AndyD87/LED-Cube-8x8x8-RGB/Software/PIC18F4520/config.h

/**
 * @file    config.h
 * @author  Andreas Dirmeier
 * @version 0.01
 *  
 * @brief   Configuration Bits and Functions for uController
 */
#ifndef CONFIG_H
#define	CONFIG_H

#include <xc.h>

// #pragma config statements should precede project file includes.
// Use project enums instead of #define for ON and OFF.

// CONFIG1H
#pragma config OSC = HS         /**< Oscillator Selection bits (HS oscillator)*/
#pragma config FCMEN = OFF      // Fail-Safe Clock Monitor Enable bit (Fail-Safe Clock Monitor disabled)*/
#pragma config IESO = OFF       /**< Internal/External Oscillator Switchover bit (Oscillator Switchover mode disabled)*/

// CONFIG2L
#pragma config PWRT = OFF       /**< Power-up Timer Enable bit (PWRT disabled)*/
#pragma config BOREN = OFF      /**< Brown-out Reset Enable bits (Brown-out Reset disabled in hardware and software)*/
#pragma config BORV = 0         /**< Brown Out Reset Voltage bits (Maximum setting)*/

// CONFIG2H
#pragma config WDT = OFF        /**< Watchdog Timer Enable bit (WDT disabled (control is placed on the SWDTEN bit))*/
#pragma config WDTPS = 32768    /**< Watchdog Timer Postscale Select bits (1:32768)*/

// CONFIG3H
#pragma config CCP2MX = PORTC   /**< CCP2 MUX bit (CCP2 input/output is multiplexed with RC1)*/
#pragma config PBADEN = OFF     /**< PORTB A/D Enable bit (PORTB<4:0> pins are configured as digital I/O on Reset)*/
#pragma config LPT1OSC = OFF    /**< Low-Power Timer1 Oscillator Enable bit (Timer1 configured for higher power operation)*/
#pragma config MCLRE = ON       /**< MCLR Pin Enable bit (MCLR pin enabled; RE3 input pin disabled)*/

// CONFIG4L
#pragma config STVREN = ON      /**< Stack Full/Underflow Reset Enable bit (Stack full/underflow will cause Reset)*/
#pragma config LVP = OFF        /**< Single-Supply ICSP Enable bit (Single-Supply ICSP disabled)*/
#pragma config XINST = ON       /**< Extended Instruction Set Enable bit (Instruction set extension and Indexed Addressing mode enabled)*/

// CONFIG5L
#pragma config CP0 = OFF        /**< Code Protection bit (Block 0 (000800-001FFFh) not code-protected)*/
#pragma config CP1 = OFF        /**< Code Protection bit (Block 1 (002000-003FFFh) not code-protected)*/

// CONFIG5H
#pragma config CPB = OFF        /**< Boot Block Code Protection bit (Boot block (000000-0007FFh) not code-protected)*/
#pragma config CPD = OFF        /**< Data EEPROM Code Protection bit (Data EEPROM not code-protected)*/

// CONFIG6L
#pragma config WRT0 = OFF       /**< Write Protection bit (Block 0 (000800-001FFFh) not write-protected)*/
#pragma config WRT1 = OFF       /**< Write Protection bit (Block 1 (002000-003FFFh) not write-protected)*/

// CONFIG6H
#pragma config WRTC = OFF       /**< Configuration Register Write Protection bit (Configuration registers (300000-3000FFh) not write-protected)*/
#pragma config WRTB = OFF       /**< Boot Block Write Protection bit (Boot block (000000-0007FFh) not write-protected)*/
#pragma config WRTD = OFF       /**< Data EEPROM Write Protection bit (Data EEPROM not write-protected)*/

// CONFIG7L
#pragma config EBTR0 = OFF      /**< Table Read Protection bit (Block 0 (000800-001FFFh) not protected from table reads executed in other blocks)*/
#pragma config EBTR1 = OFF      /**< Table Read Protection bit (Block 1 (002000-003FFFh) not protected from table reads executed in other blocks)*/

// CONFIG7H
#pragma config EBTRB = OFF      /**< Boot Block Table Read Protection bit (Boot block (000000-0007FFh) not protected from table reads executed in other blocks)*/

/**
 * @brief Load Default Configuration for the uControler 
 */ 
extern void LoadConfig();

#endif	/* CONFIG_H */
