AndyD87/LED-Cube-8x8x8-RGB/Software/PIC18F4520/cube/cube_com.h

/**
 * @file    cube_com.h
 * @author  Andreas Dirmeier
 * @version 0.01
 *  
 * @brief   Cube communication handling
 */
#ifndef _cube_com_
	#define _cube_com_

#include "../lib/SDCard.h"

extern void cube_enter_stage(unsigned char);
extern void cube_call_from_uart(unsigned char);
extern unsigned char cube_timer_interrupt();

#endif
